monofuel/handheld/v0.95/front_buttons.stl

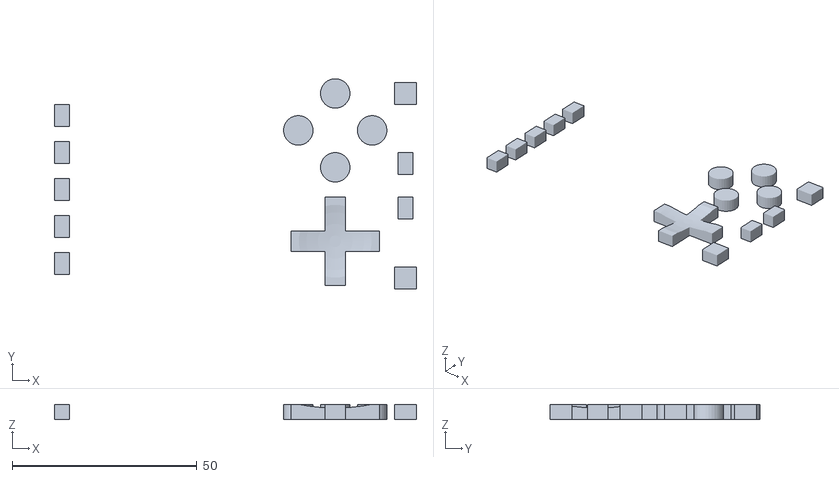
[picture p18: CAD file, 2019-10-22, an earlier design]
v0.95/front_buttons.stl
98.0 x 57.0 x 4.00
