monofuel/handheld/v0.9/LR_button.stl

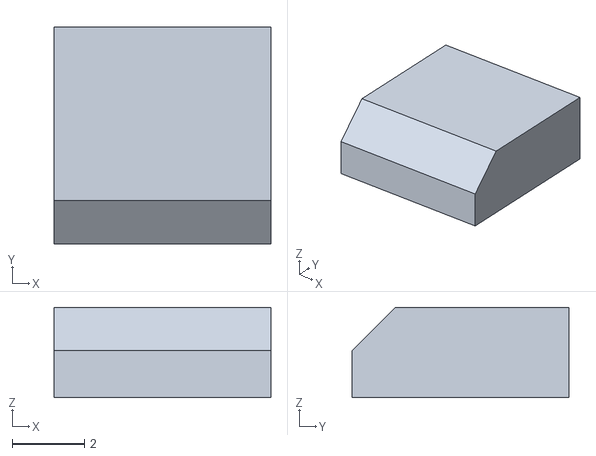
[picture p19: CAD file, 2019-03-26, an earlier design]
v0.9/LR_button.stl
6.00 x 6.00 x 2.50
