monofuel/handheld/src/back_case.scad

use <util.scad>;
use <back_buttons.scad>;

pwr_switch_offset = [98,73.5,4];

module slide_switch_cutout() {
    union() {
        // hole to contain the body of the power switch
        translate([0,0,-2])
            cube([4.2,11.7,8]);
        // hole for the 'switch' of the power switch
        translate([0.7,2.4,5])
        cube([2.7,6.2,5]);
    }
}


module pi_washers() {
    
        translate([7.5,8.5,3])
            washer(3,6);
        translate([7.5,8.5,3.7])
            screw();
        
        
         translate([56.5,8.5,3])
            washer(3,6);
        translate([56.5,8.5,3.7])
            screw();
        
        
        translate([7.5,66.5,3])
            washer(3,6);
        translate([7.5,66.5,3.7])
            screw();
        
       
         translate([56.5,66.5,3])
            washer(3,6);
        translate([56.5,66.5,3.7])
            screw();
}

module back_case() {
        // right side
        difference() {
            translate([2,72,-6])
            cube([150,8,16]);
          
            // cable cutout channel
            translate([13,71,4])
            cube([85,6,7]);
            
            // sd card cutout
            // the sd card is not removable without removing the pi
            // I found it was easy to bump and auto-eject on the pigirrl
            translate([25,71,-3])
            cube([14,3,8]);
            
            // power switch
            translate(pwr_switch_offset)
            rotate([0,90,90])
            slide_switch_cutout();
            
            // powerboost usb charging
            // larger cutout for bulky adapters
            translate([126 - 5,74,0])
            cube([15,10,11]);
            // powerboost usb charging
            // snug inner hole for the micro usb port
            translate([129.5 - 5,71,2])
            cube([8.5,7,4]);
            
            // needs to match the front of case
            // bottom right screw by power
            translate([108,75,6])
                rotate([0,180,0])
                screw_with_hole();
              // upper right screw
            translate([8,75,6])
                rotate([0,180,0])
                screw_with_hole();
        }
        
        // back side of case
        difference() {
            translate([2,3,-6])
                cube([144,69,1]);
            translate([69,21,-8]) {
                lr_button_cutout();
                translate([0,20,0]) lr_button_cutout();
                translate([12,0,0]) lr_button_cutout();
                translate([12,20,0]) lr_button_cutout();
            }
        }

        // back controller mounts
        translate([70,11,-4])
            rotate([0,180,0])
            screw_mount();
        translate([70,63,-4])
            rotate([0,180,0])
            screw_mount();

        translate([100,11,-4])
            rotate([0,180,0])
            screw_mount();
        translate([100,63,-4])
            rotate([0,180,0])
            screw_mount();

        // pi 3 A+ mounts
        translate([7.5,8.5,-4])
            rotate([0,180,0])
            screw_mount();
        translate([56.5,8.5,-4])
            rotate([0,180,0])
            screw_mount();
         translate([7.5,66.5,-4])
            rotate([0,180,0])
            screw_mount();
        translate([56.5,66.5,-4])
            rotate([0,180,0])
            screw_mount();

        $fn=30;
        // Top
        difference() {
            translate([0,-3,-6])
            cube([2,83,16]);
        
            // audio hole
            translate([0,16.5,4.5])
            rotate([0,90,0])
            cylinder(h=15, d=6.5, center=true);
            // square top of audio port for easy 3D printer bridging
            translate([0,16.5,5.5])
            cube([5,5.5,5], center=true);
            
            // hdmi
            translate([0,37.5,6])
                rotate([0,90,0])
                cube([9,15,9], center=true);
            
            // no pi micro usb hole!
            // powerboost 1000c for power wired up to pi.
    }
    
     // left side
     difference() {
            translate([2,-3,-6])
            cube([130 + 17,6,16]);
         
            translate([128,0,6])
            rotate([0,180,0])
            screw_with_hole();
            
            translate([13,0,6])
            rotate([0,180,0])
            screw_with_hole();
         
            // case hole snug around usb port
            translate([28,-3,2])
            cube([15,7,8]);
            // larger cutout around usb port for bulky connectors
            translate([35.5,-6,6])
            cube([27,15,12], center=true);
        }
        
        // powerboost mount
        // in practice I skipped installing 2 of the powerboost screws
        // I installed the 2 on the right half of the case (important for usb port)
        // but the screw holes on the board seem smaller on the left side of the powerboost
        // and the screw holes don't seem to line up anyway.
        translate([-5,0,0])
        {
            translate([142,69,-4])
                rotate([0,180,0])
                screw_mount();
            translate([125,69,-4])
                rotate([0,180,0])
                screw_mount();
            translate([140,38.2,-4])
                rotate([0,180,0])
                screw_mount();
            translate([127.5,38.2,-4])
                rotate([0,180,0])
                screw_mount();
        }

        // bottom side
        translate([132+14,-3,-6])
            cube([3,83,16]);
}

module screw_hole_reinforcement() {
    $fn=30;
    // Add 1mm wall thickness around screw holes by creating hollow rings
    // Right side screws - full height coverage
    translate([108,75,2])
        rotate([0,180,0])
        difference() {
            cylinder(h=16, d=7.8, center=true); // outer cylinder, full case height
            cylinder(h=16, d=5.8, center=true); // inner hole, full case height
        }
    
    translate([8,75,2])
        rotate([0,180,0])
        difference() {
            cylinder(h=16, d=7.8, center=true);
            cylinder(h=16, d=5.8, center=true);
        }
    
    // Left side screws  
    translate([128,0,2])
        rotate([0,180,0])
        difference() {
            cylinder(h=16, d=7.8, center=true);
            cylinder(h=16, d=5.8, center=true);
        }
    
    translate([13,0,2])
        rotate([0,180,0])
        difference() {
            cylinder(h=16, d=7.8, center=true);
            cylinder(h=16, d=5.8, center=true);
        }
}

module beveled_back_case() {
    difference() {
        union() {
            back_case();
            // Add reinforcement around screw holes
            screw_hole_reinforcement();
        }
        
        // Apply beveling to both case and reinforcement
        translate([-10,65,-8])
        rotate(45)
        cube(30);
        translate([-10,-31,-8])
        rotate(45)
        cube(30);
        
        translate([142 + 13,65,-8])
        rotate(40)
        cube(30);
        translate([145 + 13,-31,-8])
        rotate(50)
        cube(30);
        
        translate([-10,-19,-28])
        rotate([45,0,0])
        cube([200,30,30]);
        
        translate([-10,96,-28])
        rotate([45,0,0])
        cube([200,30,30]);
    }
}

beveled_back_case();
