monofuel/handheld/src/washer_3mm.scad

use <util.scad>;

washer(h=3, d=5); 
