monofuel/handheld/src/washer_4mm.scad

use <util.scad>;

washer(h=4, d=5); 
